Tengyez/wavecoustic/docs/model_pictures/back_closed.png

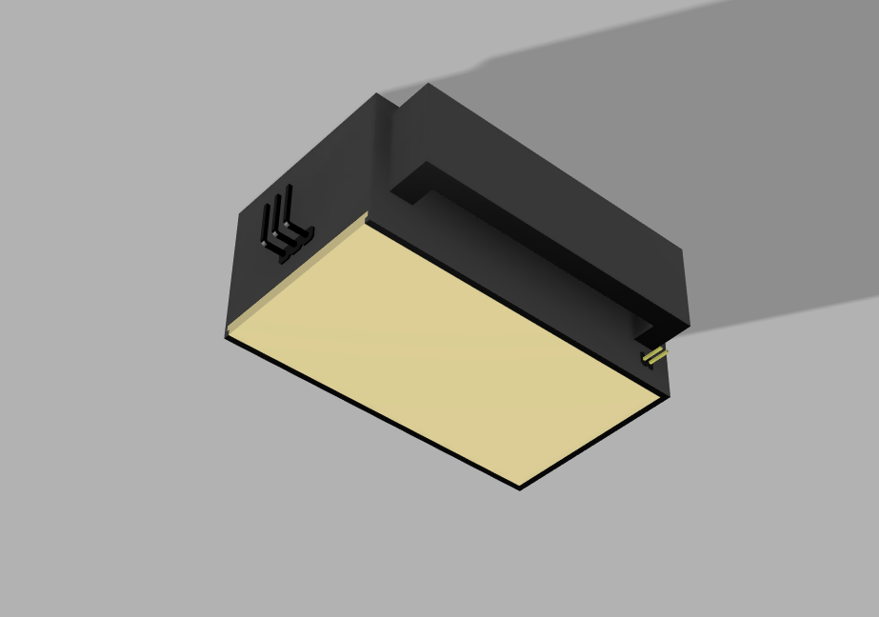
docs/model_pictures/back_closed.png
