Tengyez/wavecoustic/docs/model_pictures/closed_unrendered.png

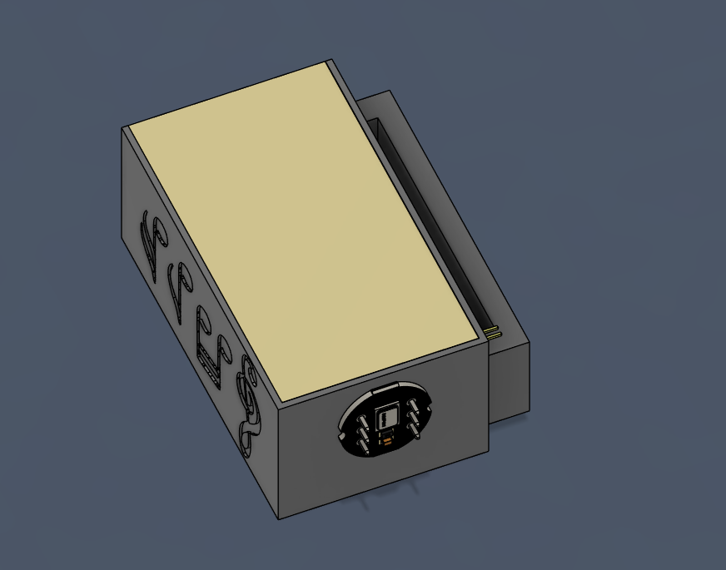
docs/model_pictures/closed_unrendered.png
