Tengyez/wavecoustic/docs/model_pictures/main_unrendered.png

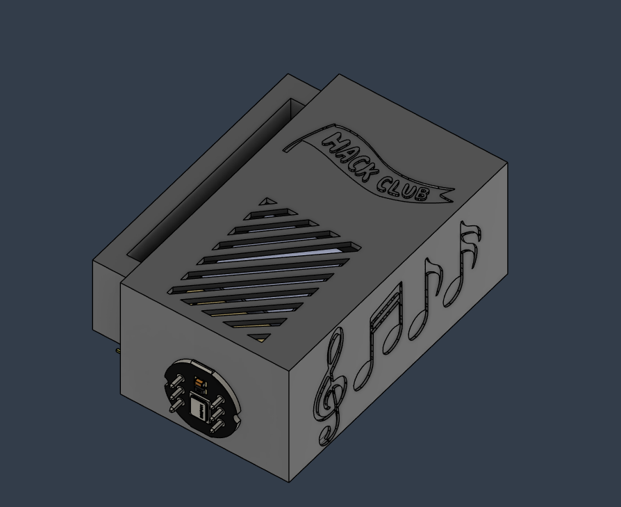
docs/model_pictures/main_unrendered.png
