Tengyez/wavecoustic/docs/model_pictures/top_back.png

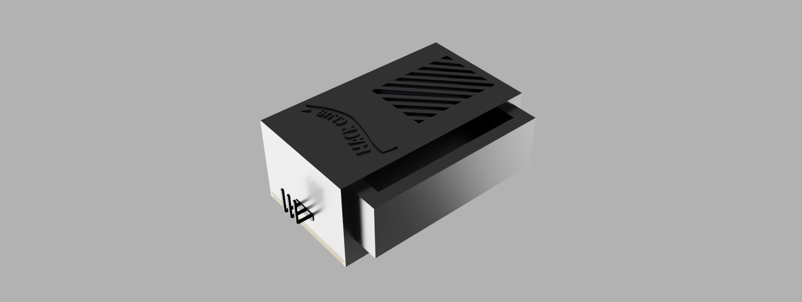
docs/model_pictures/top_back.png
