Tengyez/wavecoustic/docs/ui.png

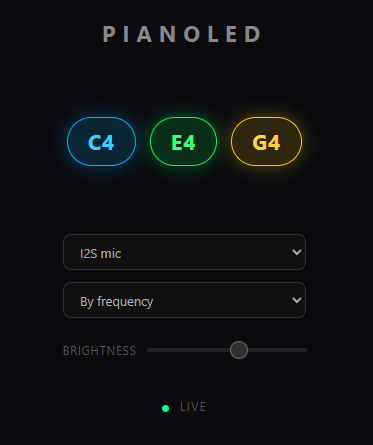
docs/ui.png
